d4niele/maia/imgs/ponte_wheatstone.jpg

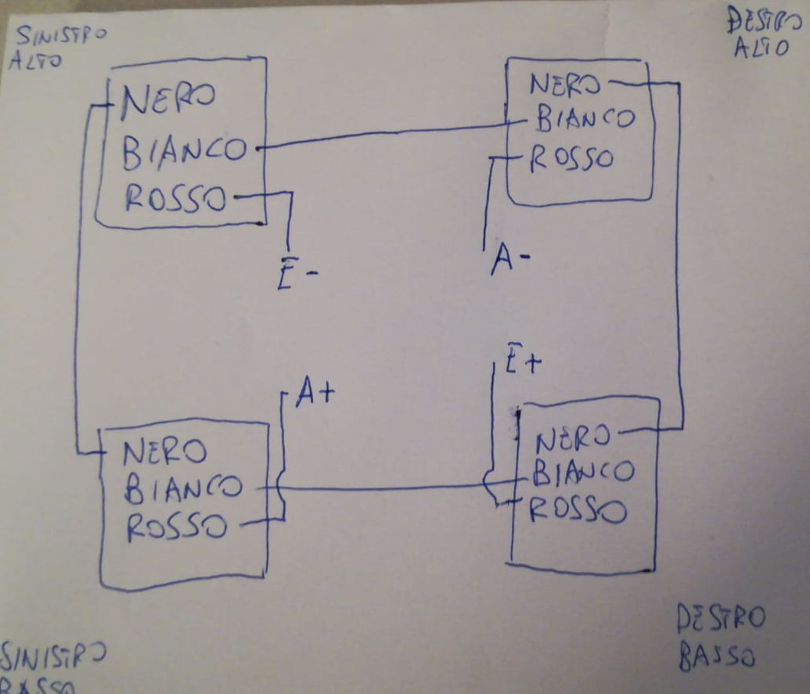
imgs/ponte_wheatstone.jpg
