d4niele/maia/imgs/proto1_load_cell.jpg

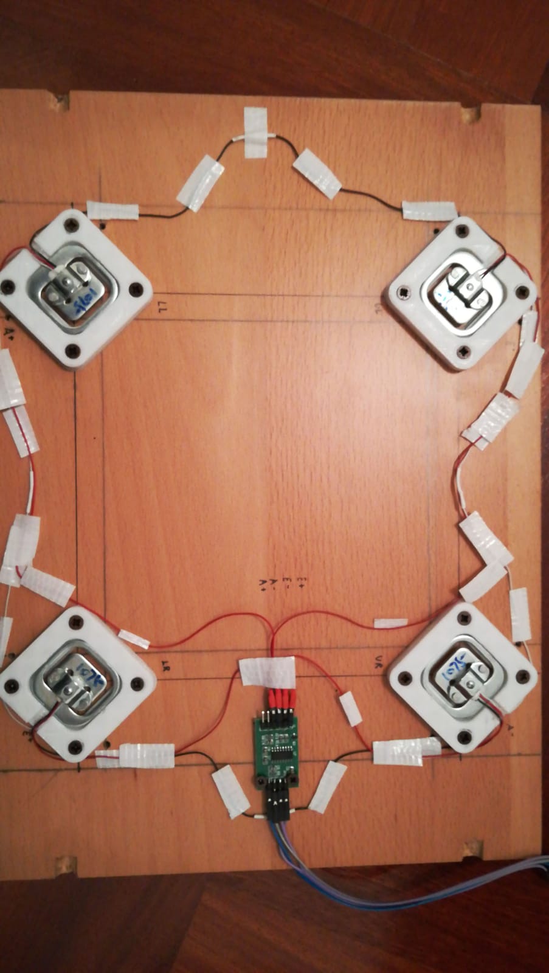
imgs/proto1_load_cell.jpg
